SparkWorksLab/ha-display/images/JLCPCB_PCB_Assy_2pcs.png

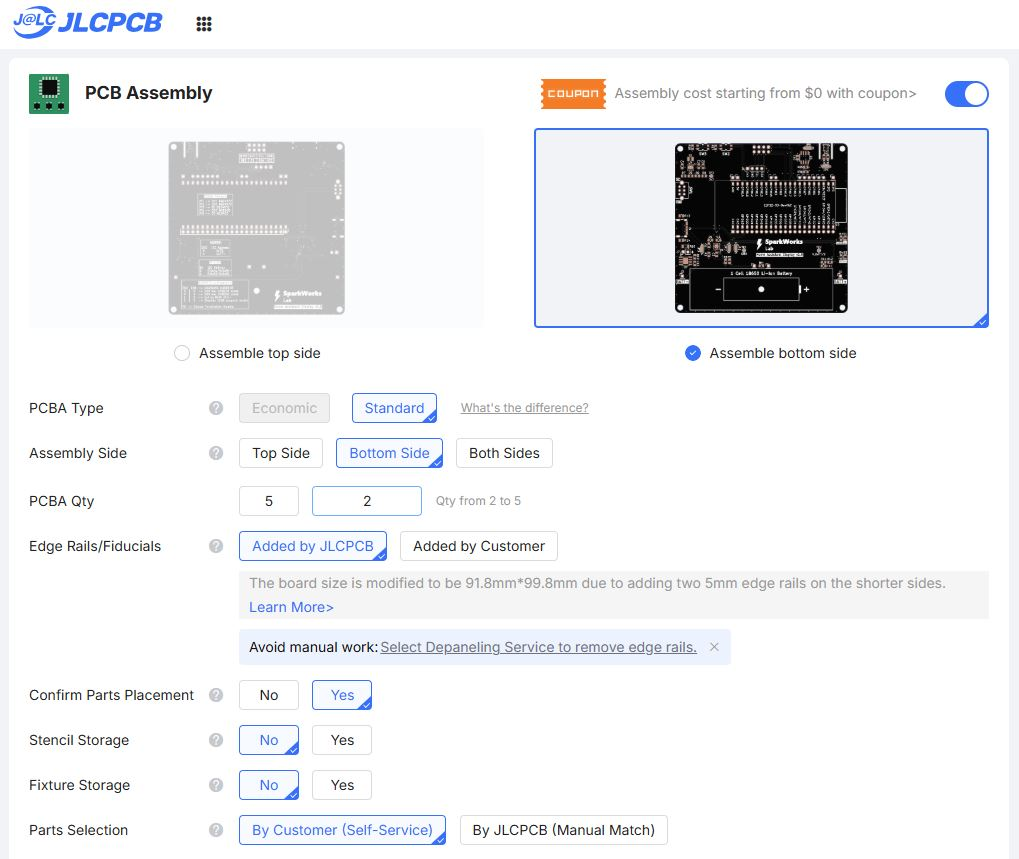
images/JLCPCB_PCB_Assy_2pcs.png
